ferauche/RoboAlegria/circuitos/imagens e vídeos/01-1.jpg

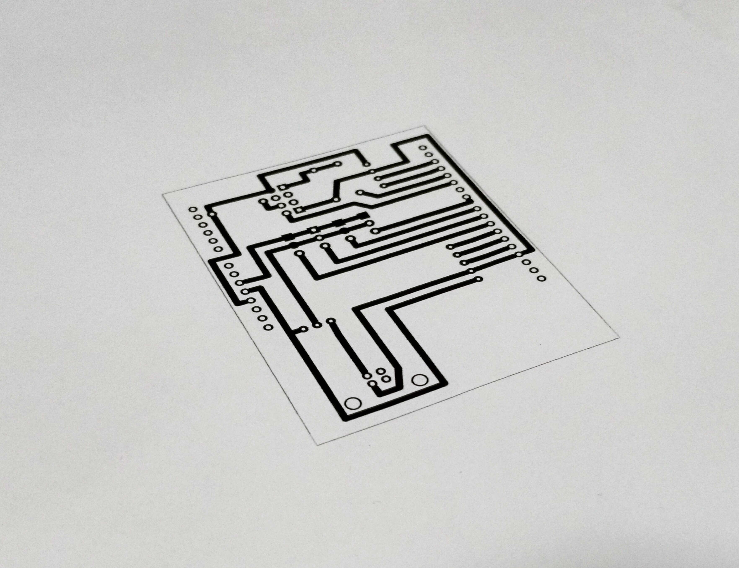
circuitos/imagens e vídeos/01-1.jpg
