ferauche/RoboAlegria/circuitos/imagens e vídeos/02-1.jpg

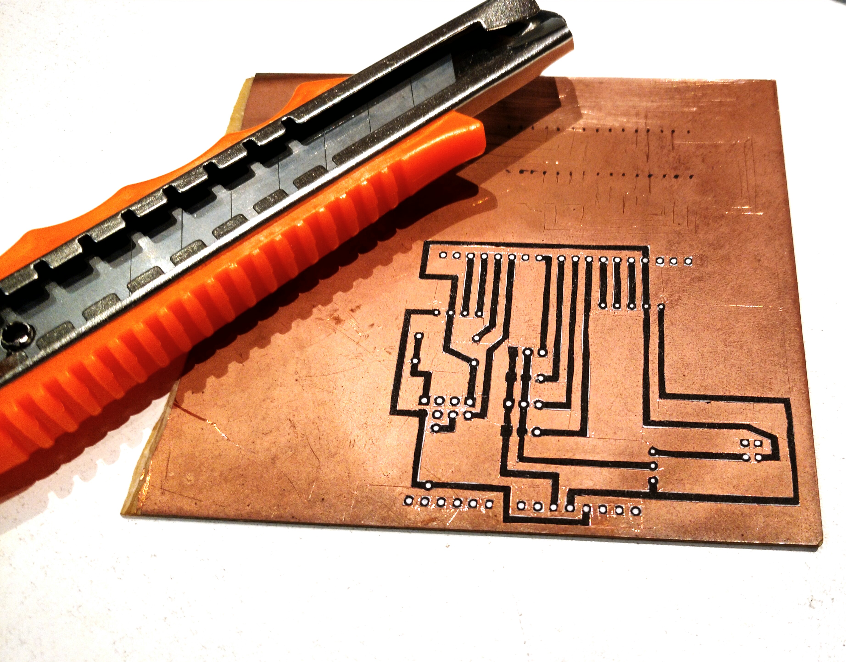
circuitos/imagens e vídeos/02-1.jpg
