ferauche/RoboAlegria/circuitos/imagens e vídeos/03-1.jpg

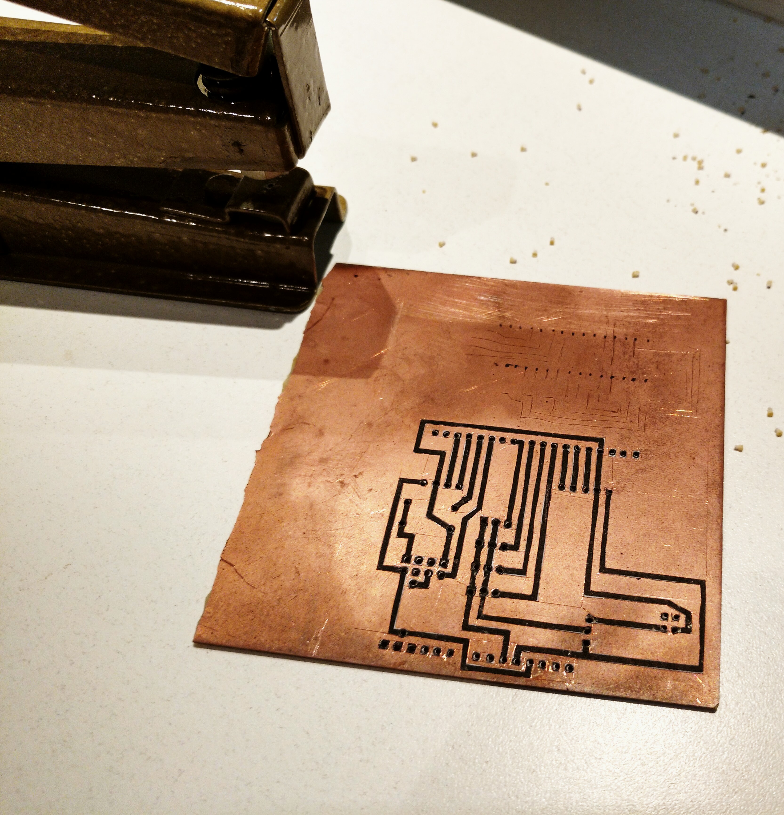
circuitos/imagens e vídeos/03-1.jpg
