ferauche/RoboAlegria/circuitos/imagens e vídeos/04-1.jpg

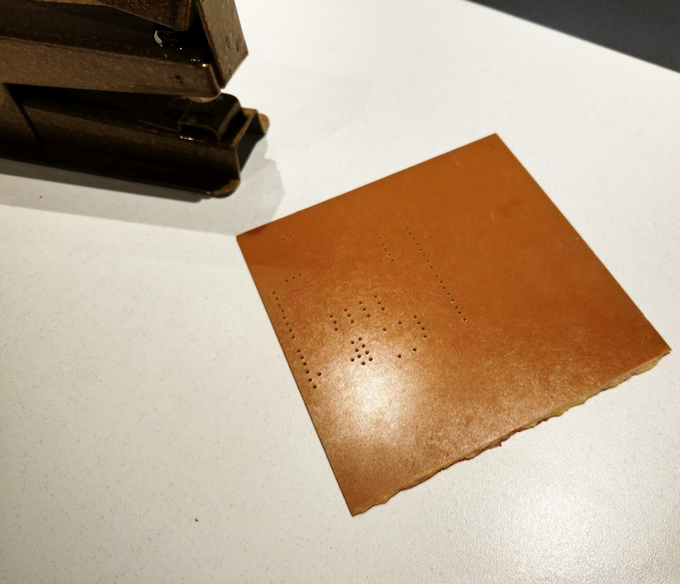
circuitos/imagens e vídeos/04-1.jpg
