ferauche/RoboAlegria/circuitos/imagens e vídeos/05-1.jpg

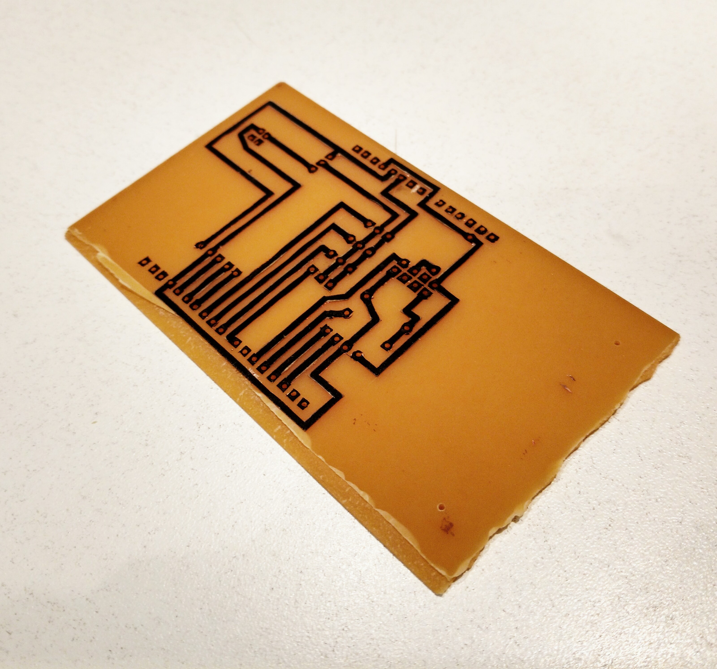
circuitos/imagens e vídeos/05-1.jpg
