ferauche/RoboAlegria/circuitos/imagens e vídeos/06-1.jpg

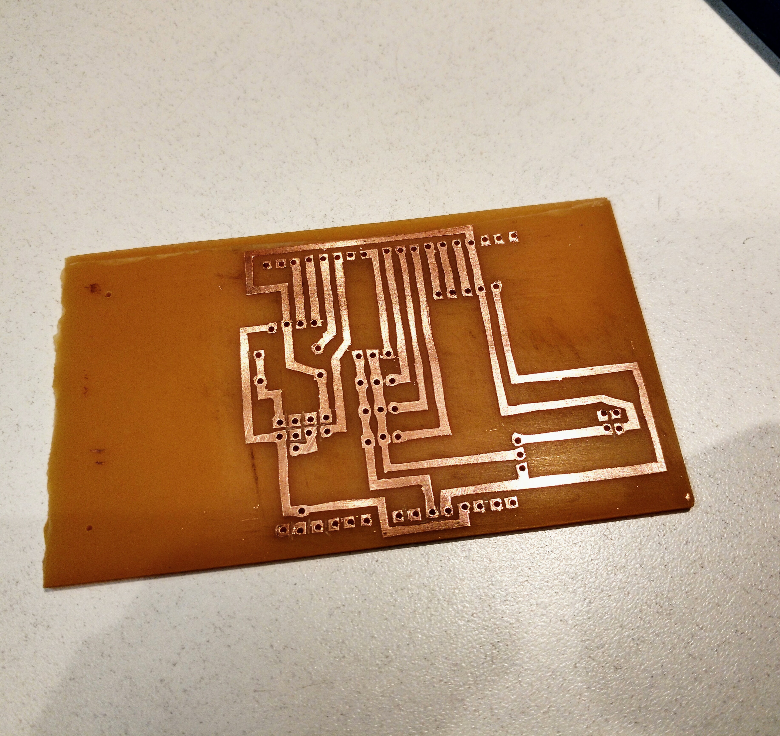
circuitos/imagens e vídeos/06-1.jpg
