ferauche/RoboAlegria/circuitos/imagens e vídeos/07-1.jpg

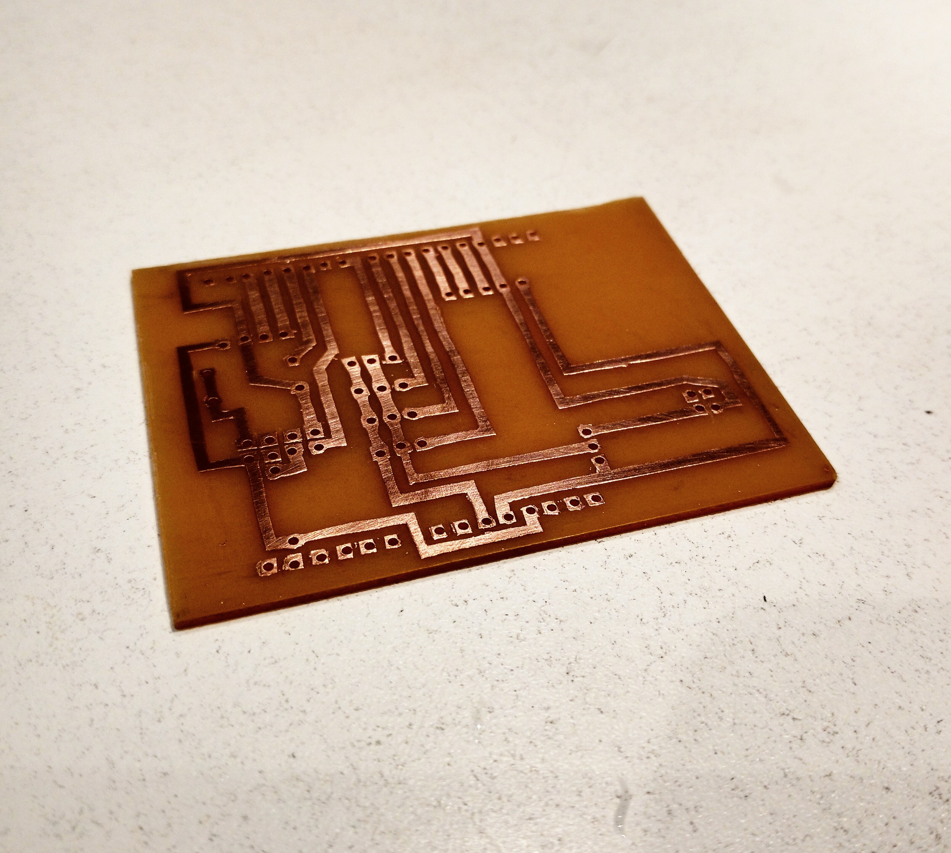
circuitos/imagens e vídeos/07-1.jpg
