ferauche/RoboAlegria/circuitos/imagens e vídeos/08-1.jpg

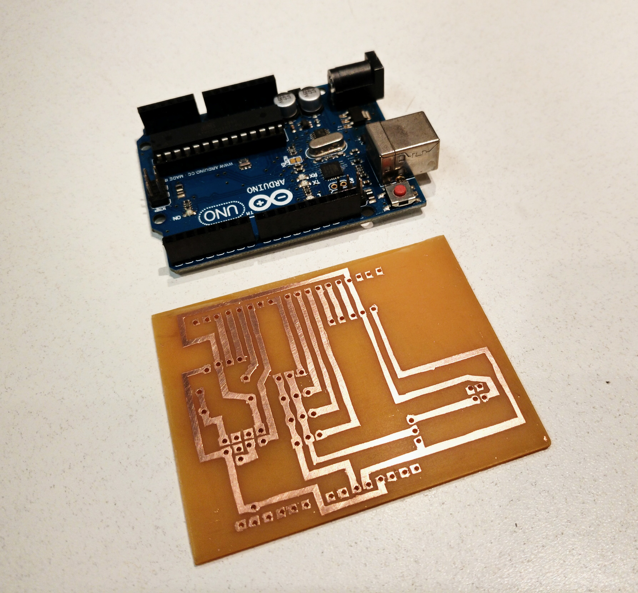
circuitos/imagens e vídeos/08-1.jpg
