ferauche/RoboAlegria/circuitos/imagens e vídeos/09-1.jpg

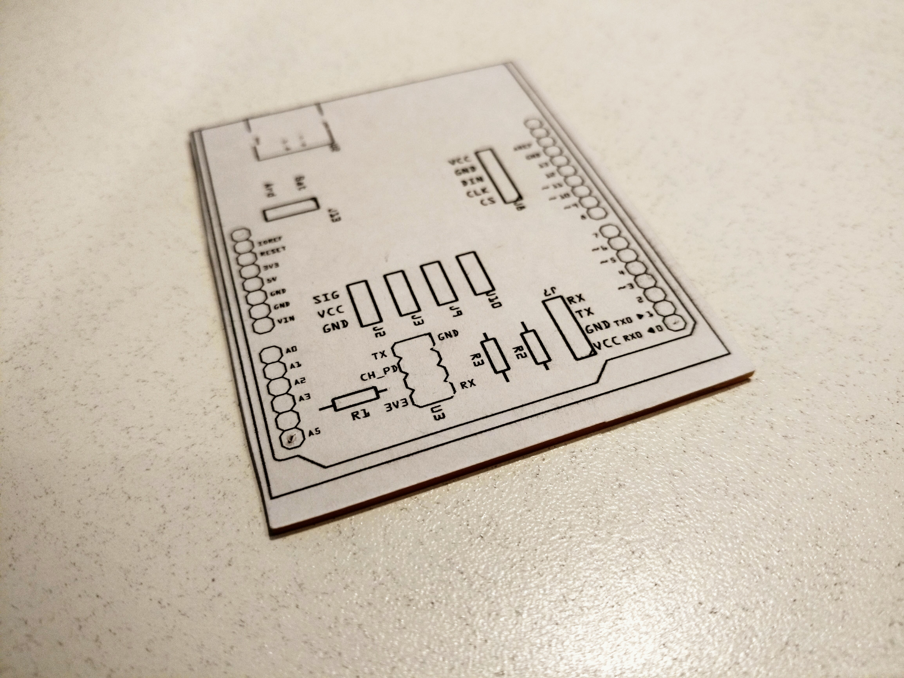
circuitos/imagens e vídeos/09-1.jpg
