ferauche/RoboAlegria/circuitos/imagens e vídeos/10-1.jpg

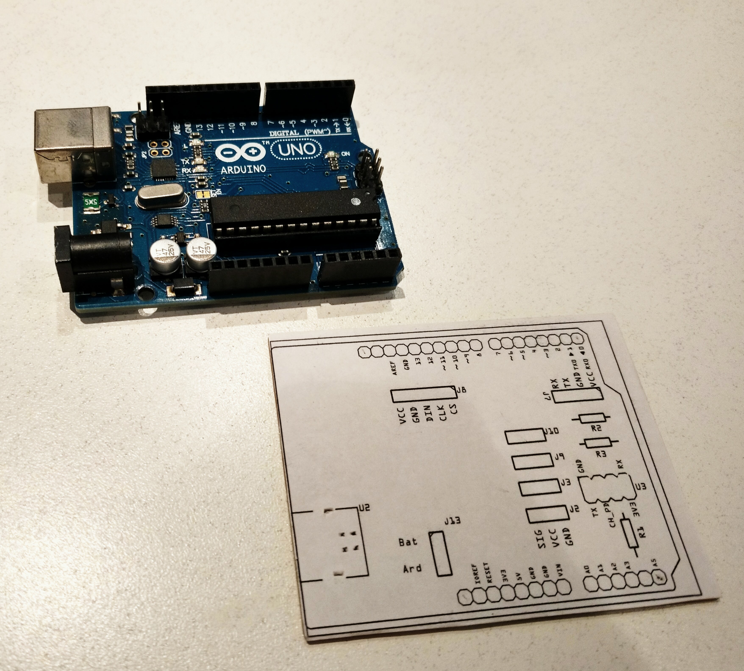
circuitos/imagens e vídeos/10-1.jpg
