ferauche/RoboAlegria/circuitos/imagens e vídeos/11-1.jpg

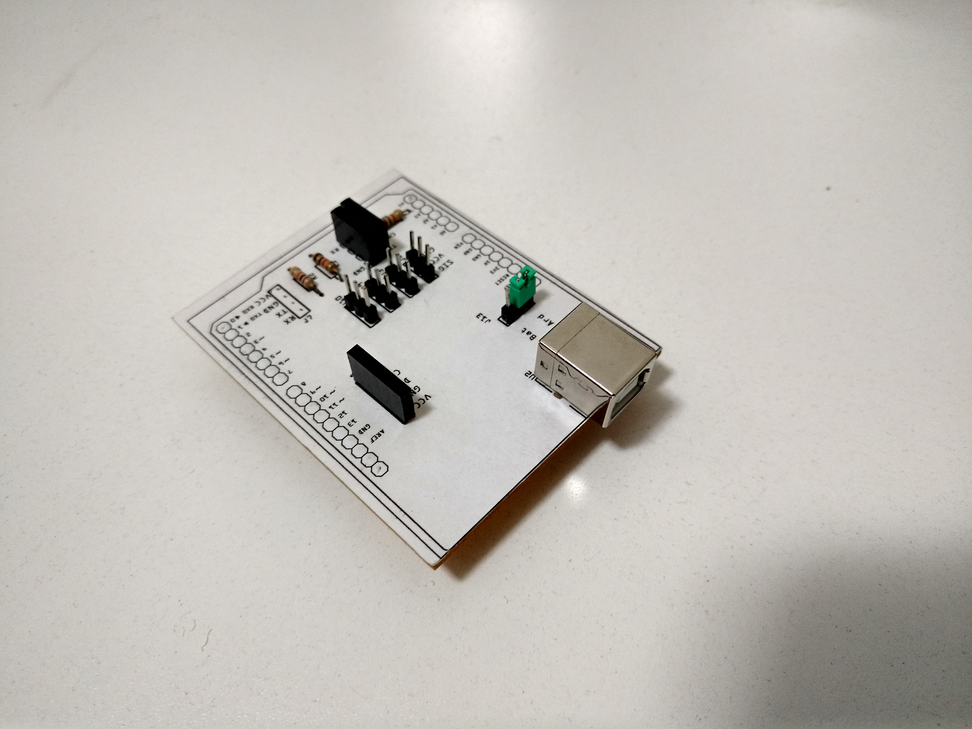
circuitos/imagens e vídeos/11-1.jpg
