ferauche/RoboAlegria/circuitos/imagens e vídeos/12-1.jpg

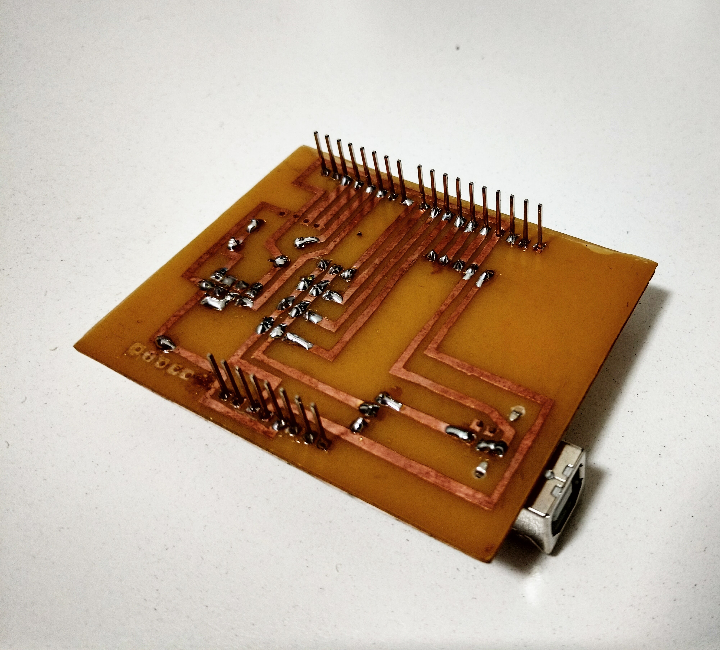
circuitos/imagens e vídeos/12-1.jpg
