ferauche/RoboAlegria/circuitos/imagens e vídeos/13-1.jpg

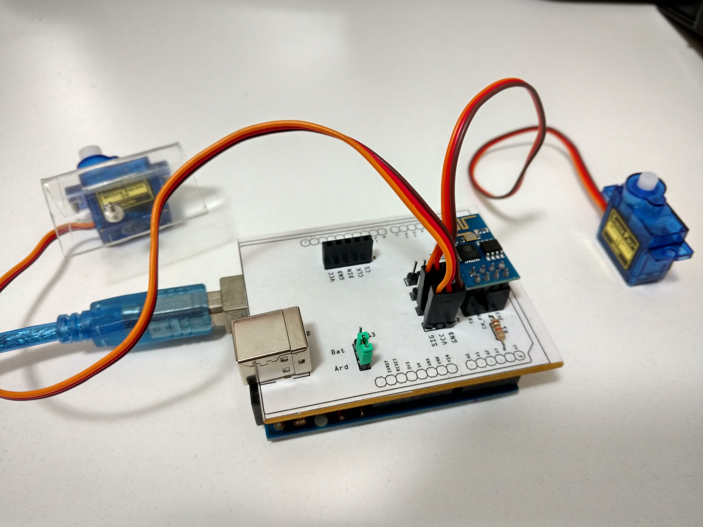
circuitos/imagens e vídeos/13-1.jpg
