ferauche/RoboAlegria/circuitos/imagens e vídeos/14-1.jpg

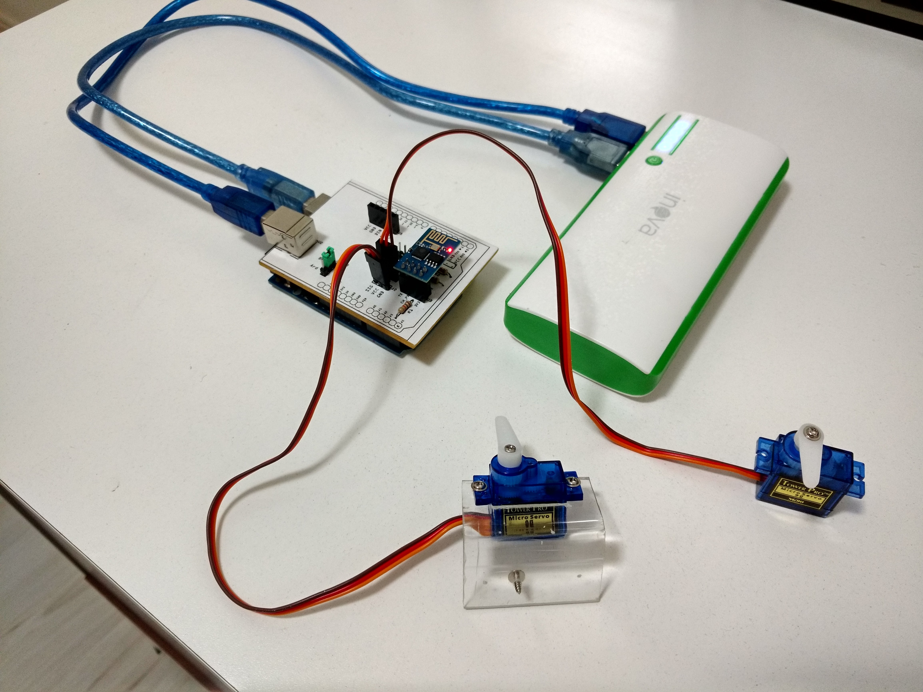
circuitos/imagens e vídeos/14-1.jpg
